MagZu/OpenFrEON/giraffe/honda/bosch/bosch_male.stl

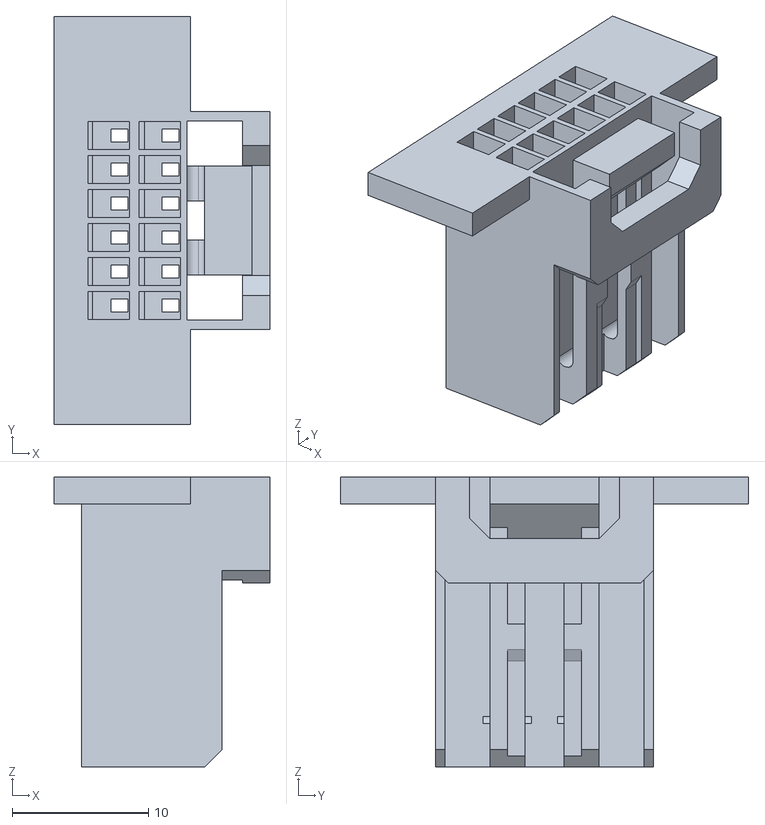
[picture p19: CAD file, 2019-07-03]
giraffe/honda/bosch/bosch_male.stl
15.9 x 30.0 x 21.3
