MagZu/OpenFrEON/giraffe/subaru/PIP_left.stl

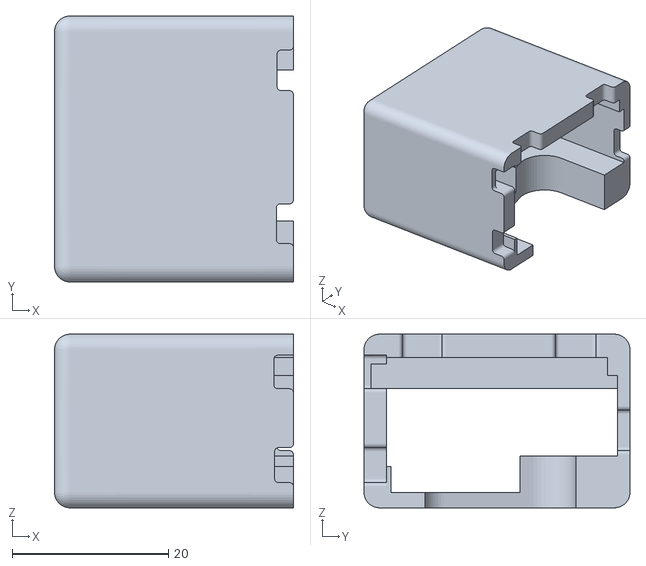
[picture p20: CAD file, 2019-07-03]
giraffe/subaru/PIP_left.stl
30.6 x 34.1 x 22.3
