MagZu/OpenFrEON/gopro mount/gopro2.STL

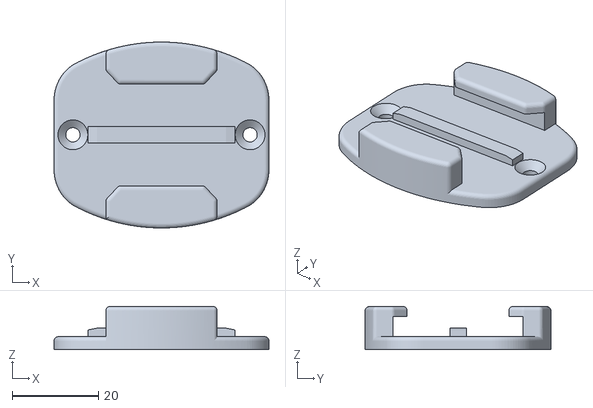
[picture p21: CAD file, 2019-07-03]
gopro mount/gopro2.STL
49.8 x 43.0 x 10.0
