MagZu/OpenFrEON/oneplus 3t/FrEON2EM-Right.stl

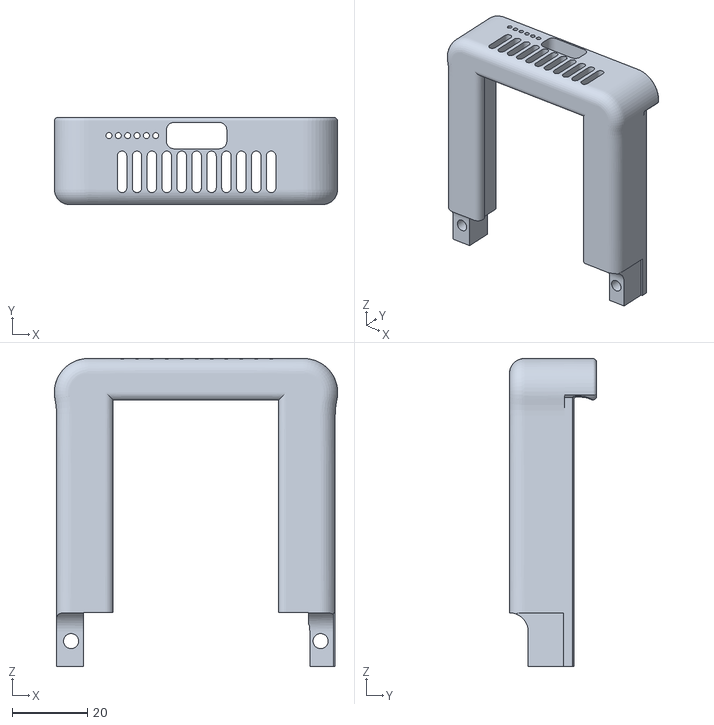
[picture p22: CAD file, 2019-06-25]
oneplus 3t/FrEON2EM-Right.stl
75.1 x 23.1 x 81.6
