MagZu/OpenFrEON/pedal/pedal.stl

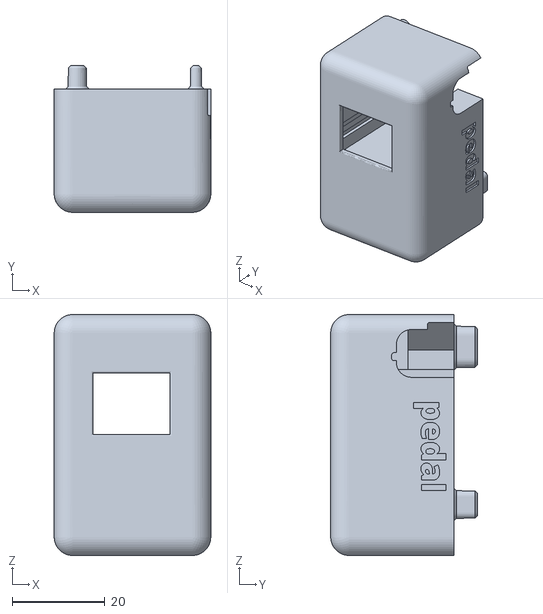
[picture p23: CAD file, 2019-07-03]
pedal/pedal.stl
33.8 x 31.7 x 52.0
