MagZu/OpenFrEON/Tinkla Buddy nordic/Tinkla Buddy Nordic_top v12.stl

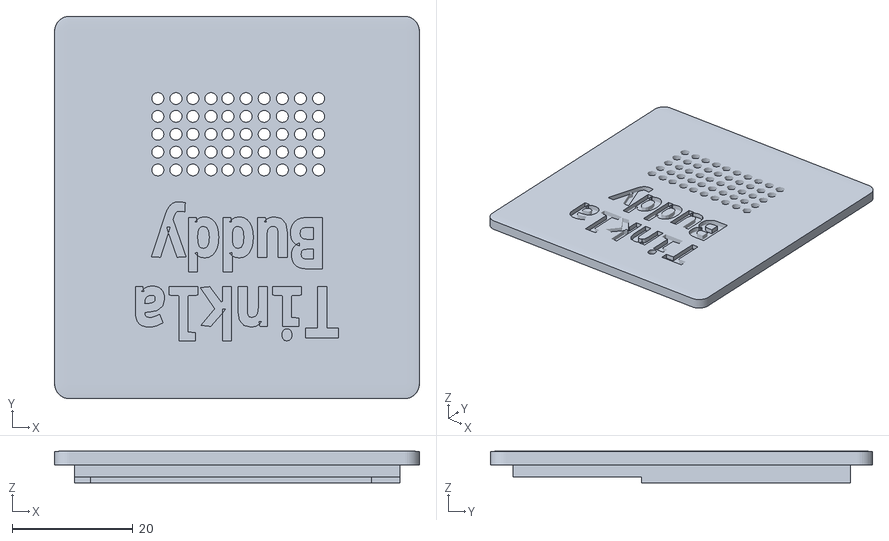
[picture p24: CAD file, 2021-04-15]
Tinkla Buddy nordic/Tinkla Buddy Nordic_top v12.stl
60.4 x 63.3 x 5.29
