MagZu/OpenFrEON/giraffe/ford/mechanical/giraffe_ford_bottom.stl

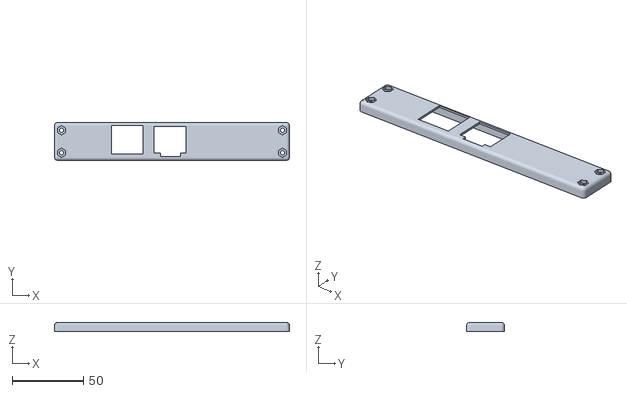
[picture p25: CAD file, 2019-07-03]
giraffe/ford/mechanical/giraffe_ford_bottom.stl
164.5 x 26.4 x 6.57
