MagZu/OpenFrEON/giraffe/honda/bosch/bosch_back.stl

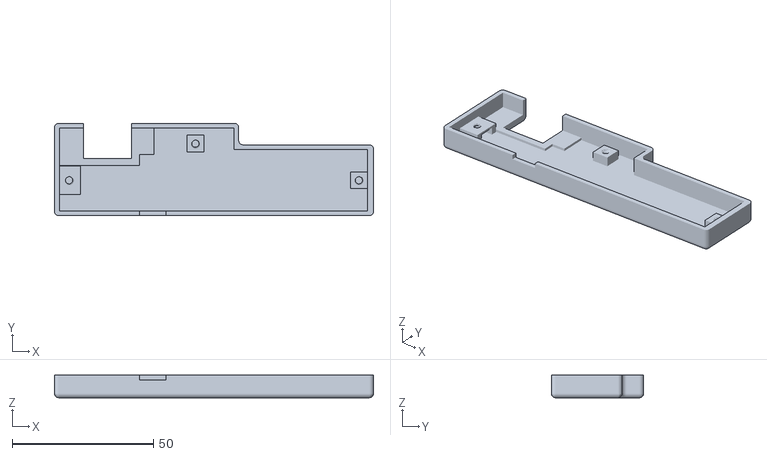
[picture p26: CAD file, 2019-07-03]
giraffe/honda/bosch/bosch_back.stl
113.0 x 32.7 x 8.00
