MagZu/OpenFrEON/leeco lepro3 x720/Right Case.STL

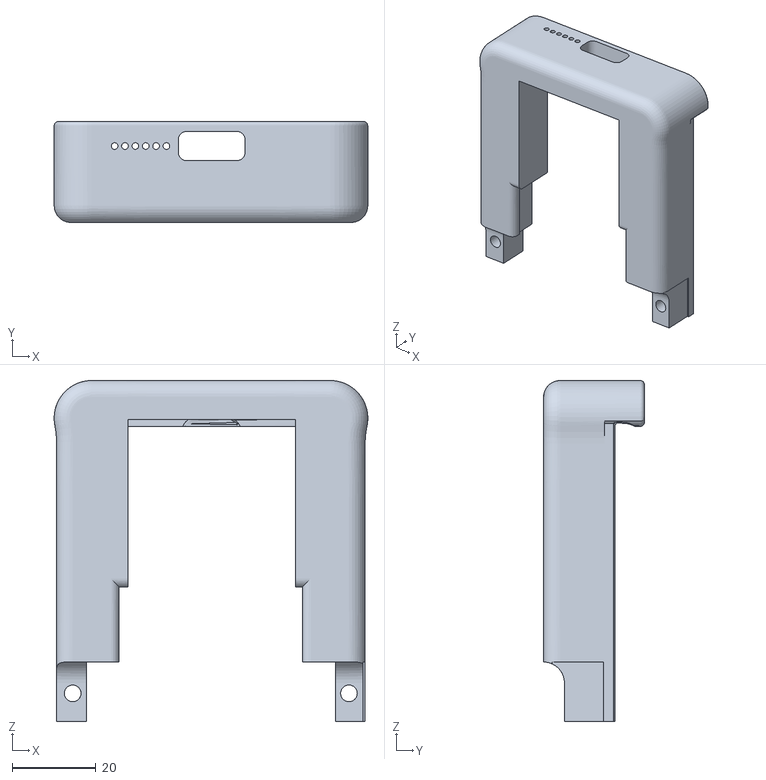
[picture p27: CAD file, 2019-06-25]
leeco lepro3 x720/Right Case.STL
75.1 x 24.2 x 81.6
