MagZu/OpenFrEON/oneplus 3t/FrEON2EM-Left.stl

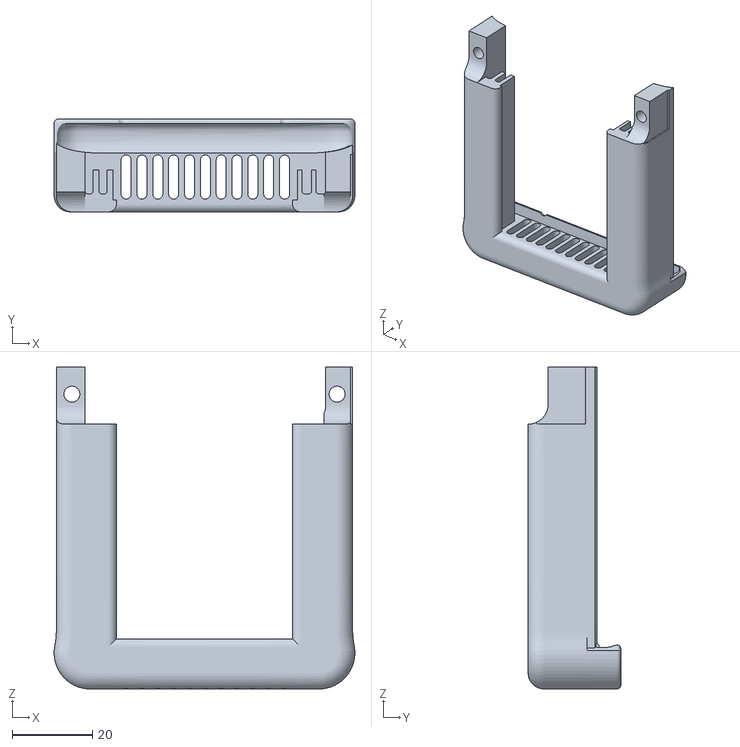
[picture p28: CAD file, 2019-06-25]
oneplus 3t/FrEON2EM-Left.stl
75.0 x 23.1 x 80.3
