MagZu/OpenFrEON/pedal/pedal_connector.stl

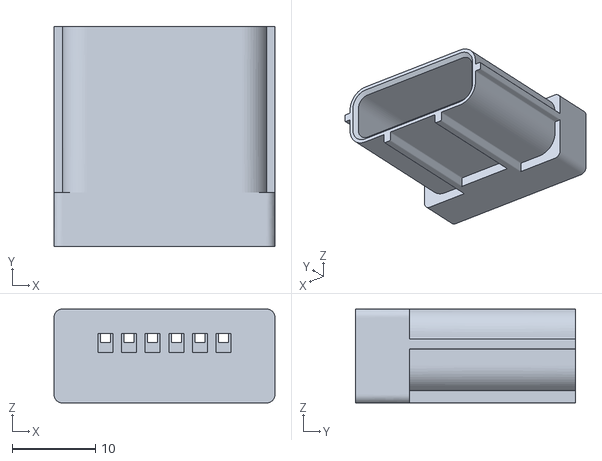
[picture p29: CAD file, 2019-07-03]
pedal/pedal_connector.stl
26.6 x 26.5 x 11.3
