MagZu/OpenFrEON/giraffe/honda/bosch/bosch_front.stl

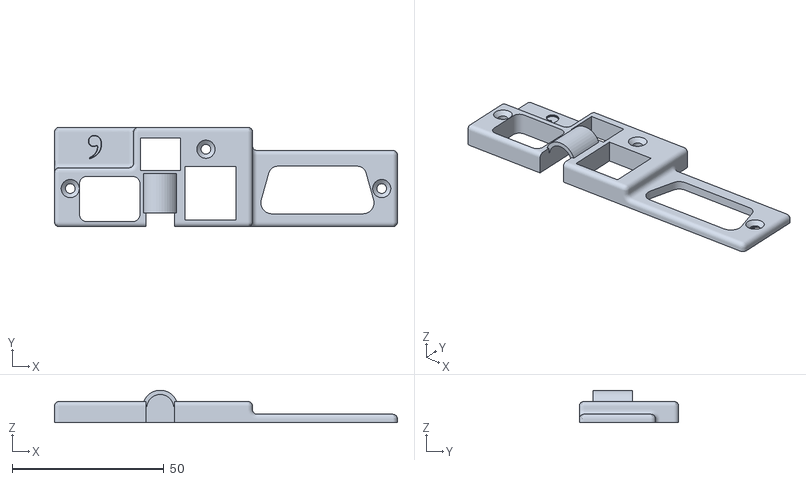
[picture p30: CAD file, 2019-07-03]
giraffe/honda/bosch/bosch_front.stl
113.0 x 32.7 x 10.7
