MagZu/OpenFrEON/leeco lepro3 x720/BottomClip.stl

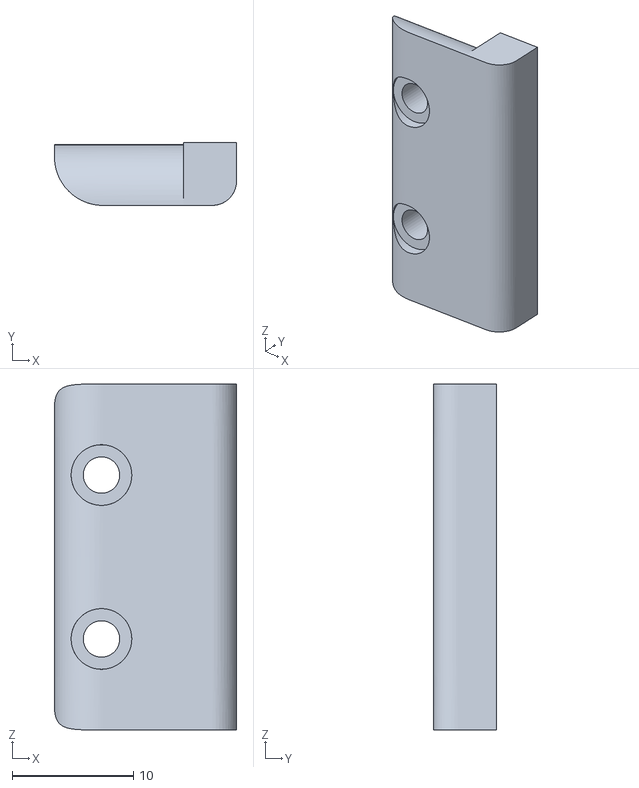
[picture p31: CAD file, 2019-06-25]
leeco lepro3 x720/BottomClip.stl
15.0 x 5.18 x 28.5
