MagZu/OpenFrEON/leeco lepro3 x720/Left Case.STL

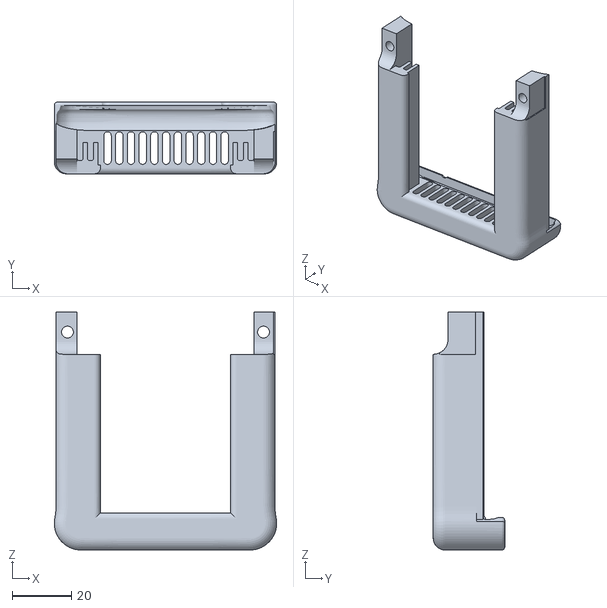
[picture p32: CAD file, 2019-06-25]
leeco lepro3 x720/Left Case.STL
75.0 x 24.2 x 80.3
